mhlsf/Raptor-led/images/Bottom.PNG

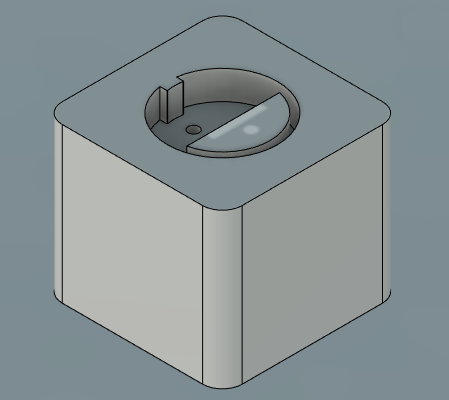
images/Bottom.PNG
