mhlsf/Raptor-led/images/readme/Image1.PNG

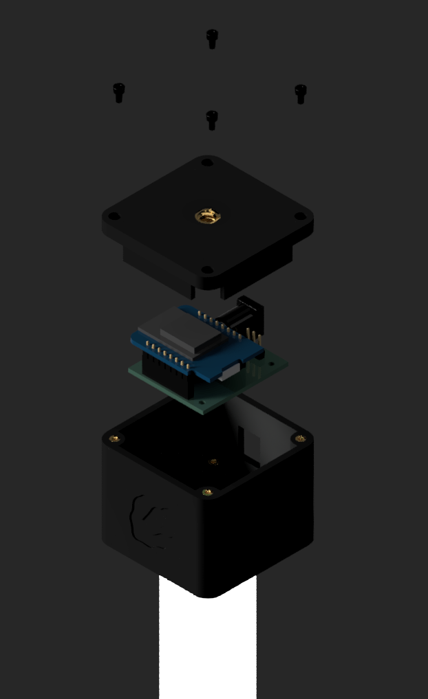
images/readme/Image1.PNG
